Tobias0110/EVN_Kaifa_ESP_MQTT/Interface_PCB/MBus_to_radio_V3/Pictures/3.png

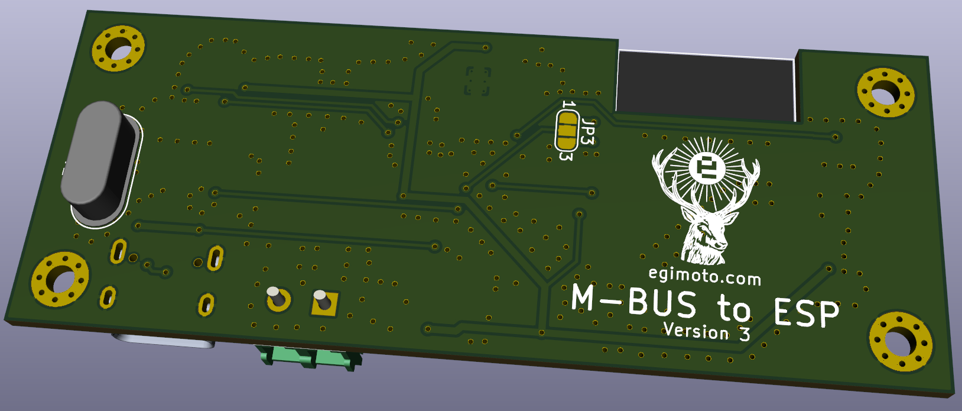
Interface_PCB/MBus_to_radio_V3/Pictures/3.png
